AdamTomaja/homenet/motion-sensor/motion-sensor.sch

## EAGLE design motion-sensor/motion-sensor.sch (2017-09-02)

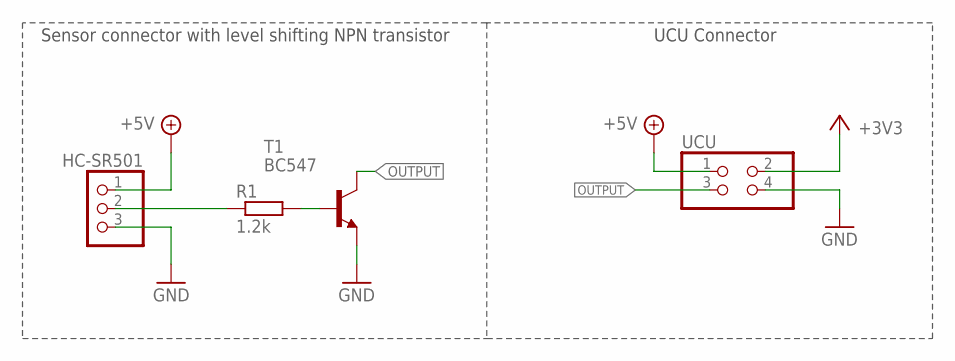
[picture p12: schematic motion-sensor.sch]

Parts:
HC-SR501: PINHD-1X3; 1X03
R1: 1.2k; 0204/7
T1: BC547; TO92
UCU: PINHD-2X2; 2X02

Connections:
+3V3: UCU.2
+5V: HC-SR501.1, UCU.1
GND: HC-SR501.3, T1.1 (E), UCU.4
unnamed: R1.2, T1.2 (B)
unnamed: HC-SR501.2, R1.1
OUTPUT: T1.3 (C), UCU.3

Notes on the sheet:
Sensor connector with level shifting NPN transistor
UCU Connector
