AdamTomaja/homenet/homenet-server/src/main/java/com/cydercode/homenet/server/rest/ValueConverter.java

package com.cydercode.homenet.server.rest;

import com.cydercode.homenet.cdm.GpioMode;
import com.cydercode.homenet.server.config.GpioConfiguration;
import com.google.common.collect.ImmutableMap;

import java.awt.*;
import java.util.Map;
import java.util.Objects;


public class ValueConverter {

    public static final String ON = "ON";
    public static final String OFF = "OFF";

    static final int SERIESRESISTOR = 10000;
    static final int NOMINAL_RESISTANCE = 10000;
    static final int NOMINAL_TEMPERATURE = 25;
    static final int BCOEFFICIENT = 3950;

    public static Object convertToUIValue(GpioConfiguration gpio, Object systemValue) {
        if (systemValue == null) {
            return systemValue;
        }

        if (gpio.getMode() == GpioMode.ANALOG_OUTPUT) {
            return systemValue;
        }

        if (gpio.getMode() == GpioMode.RGB_STRIP) {
            Map<String, Double> map = (Map) systemValue;
            Color color = new Color(map.get("r").intValue(), map.get("g").intValue(), map.get("b").intValue());
            return toHex(color.getRed(), color.getGreen(), color.getBlue());
        }

        if (gpio.getMode() == GpioMode.ANALOG_INPUT) {
            if ("temperature".equals(gpio.getDisplayAs())) {
                return convertRawADCToTemperature((Double) systemValue) + " ℃";
            } else if ("voltage".equals(gpio.getDisplayAs())) {
                return convertRawADCToVoltage((Double) systemValue) + " V";
            } else {
                return systemValue;
            }
        }

        Object value = Objects.equals(0d, systemValue) ? OFF : ON;

        if (gpio.getInvert()) {
            if (value.equals(ON)) {
                value = OFF;
            } else {
                value = ON;
            }
        }

        return value;
    }

    public static String toHex(int r, int g, int b) {
        return "#" + toBrowserHexValue(r) + toBrowserHexValue(g) + toBrowserHexValue(b);
    }

    private static String toBrowserHexValue(int number) {
        StringBuilder builder = new StringBuilder(Integer.toHexString(number & 0xff));
        while (builder.length() < 2) {
            builder.append("0");
        }
        return builder.toString().toUpperCase();
    }

    private static double convertRawADCToVoltage(double rawADC) {
        return roundToDecimalPlaces(rawADC / 1024 * 3.3, 3);
    }

    private static double convertRawADCToTemperature(double rawAdc) {
        double resistance;
        double steinhart;

        resistance = (1023 / rawAdc) - 1;
        resistance = SERIESRESISTOR / resistance;

        steinhart = resistance / NOMINAL_RESISTANCE; // (R/Ro)
        steinhart = Math.log(steinhart); // ln(R/Ro)
        steinhart /= BCOEFFICIENT; // 1/B * ln(R/Ro)
        steinhart += 1.0 / (NOMINAL_TEMPERATURE + 273.15); // + (1/To)
        steinhart = 1.0 / steinhart; // Invert
        steinhart -= 273.15; // convert to C
        return roundToDecimalPlaces(steinhart, 3);
    }

    private static double roundToDecimalPlaces(double value, int decimalPlaces) {
        double factor = Math.pow(10, decimalPlaces);
        return Math.round(value * factor) / factor;
    }

    public static Object convertToSystemValue(GpioConfiguration gpioConfiguration, Object uiValue) {
        if (gpioConfiguration.getMode() == GpioMode.ANALOG_OUTPUT) {
            return uiValue;
        }

        if (gpioConfiguration.getMode() == GpioMode.RGB_STRIP) {
            Color color = Color.decode((String) uiValue);
            return ImmutableMap.builder()
                    .put("r", color.getRed())
                    .put("g", color.getGreen())
                    .put("b", color.getBlue())
                    .build();
        }

        return Objects.equals(ON, uiValue) ? 1 : 0;
    }
}
