AdamTomaja/homenet/homenet-server/src/main/java/com/cydercode/homenet/server/ConfigurationService.java

package com.cydercode.homenet.server;

import com.cydercode.homenet.server.config.Configuration;
import com.cydercode.homenet.server.config.GpioConfiguration;
import com.cydercode.homenet.server.config.UcuInstance;
import com.google.gson.Gson;
import org.slf4j.Logger;
import org.slf4j.LoggerFactory;
import org.springframework.beans.factory.annotation.Value;
import org.springframework.stereotype.Service;

import javax.annotation.PostConstruct;
import java.io.InputStreamReader;
import java.util.Optional;

@Service
public class ConfigurationService {

    private static final Logger LOGGER = LoggerFactory.getLogger(ConfigurationService.class);

    private final Gson gson = new Gson();

    private Configuration configuration;

    @Value("${environment:default}")
    private String environment;

    @PostConstruct
    public void init() {
        String filename = "configuration/" + environment + ".json";
        InputStreamReader jsonReader = new InputStreamReader(this.getClass()
                .getClassLoader()
                .getResourceAsStream(filename));

        configuration = gson.fromJson(jsonReader, Configuration.class);

        LOGGER.info("Configuration loaded from: {}", filename);
    }

    public void createInstance(UcuInstance ucuInstance) {
        configuration.getInstances().add(ucuInstance);
    }

    public Optional<UcuInstance> getConfigurationByName(String instanceName) {
        return configuration.getInstances()
                .stream()
                .filter(instance -> instanceName.equals(instance.getName()))
                .findFirst();
    }

    public Optional<UcuInstance> getConfiguration(String instanceId) {
        return configuration.getInstances()
                .stream()
                .filter(instance -> instanceId.equals(instance.getId()))
                .findFirst();
    }

    public Configuration getConfiguration() {
        return configuration;
    }

    public void createGpio(UcuInstance ucuInstance, GpioConfiguration gpioConfiguration) {
        ucuInstance.getGpios().add(gpioConfiguration);
    }
}
